sparkfun/SparkFun_Thing_Plus_NORA-W306/docs/more_examples.md

Of course, this only skims the surface of what the SparkFun Thing Plus - NORA-W306 can do. There are a handful of examples from the board support package that were not highlighted in this tutorial and are being ported by our friends at Realtek with the NORA-W306 module. From the menu, try opening the other examples listed for hte board: **File** > **Examples** > <font style="color:gray">Examples for AW_CU488 Thing Plus (RTL8721DM)</font>

<div style="text-align: center;">
  <table>
    <tr style="vertical-align:middle;">
     <td style="text-align: center; vertical-align: middle; border: solid 1px #cccccc;"><a href="../assets/img/AmebaD_RealTek_Additional_Arduino_Examples.JPG">More Arduino Examples!</a></td>
    </tr>
    <tr style="vertical-align:middle;">
     <td style="text-align: center; vertical-align: middle; border: solid 1px #cccccc;"><i>More Arduino Examples!</i></td>
   </tr>
  </table>
</div>

!!! note
    Some of the examples listed in the menu may still be under development. Make sure to be patient as they include more support for the NORA-W306 module.

Or try adding another [Qwiic-enabled device](https://www.sparkfun.com/qwiic) or a breakout board to your next project!

<div style="text-align: center"><a href="https://www.sparkfun.com/qwiic" class="md-button md-button--primary">Qwiic Connect System</a></div>
