sparkfun/SparkFun_Thing_Plus_NORA-W306/docs/github/contribute.md

# Contribute: Help Fix our Mistake!
Spot something wrong? Feel free to contribute our open-source design and documentation. 

## Improve our Documentation
All of this documentation can be modified by you! Please help us make it better.

* These pages are contained in the [`docs` folder of the SparkFun Thing Plus NORA-W306 repository](https://github.com/sparkfun/SparkFun_Thing_Plus_NORA-W306/tree/main/docs).

### Submit a Correction
1. Fork this repo
2. Add your corrections or improvements to the markdown file
3. File a pull request with your changes, and enjoy making the ~~words~~ ~~worlds~~ world a better place.
    * Once received, the documentation specialist will automatically be notified.
    * We will review your suggested improvements to make sure they are correct and fit within our documentation standards.

## Improve our Hardware Design
All of our designs are open-source! Please help us make it better.

* Our board design files are contained in the [`Hardware` folder of the SparkFun Thing Plus NORA-W306 repository](https://github.com/sparkfun/SparkFun_Thing_Plus_NORA-W306/tree/main/Hardware).

### Submit a Design Improvement
1. Fork this repo
2. Add your design improvements
3. File a pull request with your changes, and enjoy making the ~~words~~ ~~worlds~~ world a better place.
    * Once received, the engineer in charge of the original design will automatically be notified.
    * We will review your suggested improvements, if they are within our board design standards and meet our product design requirements, we will flag these changes for our next board revision. *(Please note, that even if your suggestion is accepted, these changes may not be immediate. We may have to cycle through our current product inventory first.)*

## Contributors
Let's provided some recognition to the contributors for this project!

GitHub Contributors Image
<br>
