sparkfun/SparkFun_Thing_Plus_NORA-W306/docs/assets/img/LiPo_Fuel_Gauge_MAX1704X_Qwiic_Cable_Micro_OLED_Output_Display.jpg

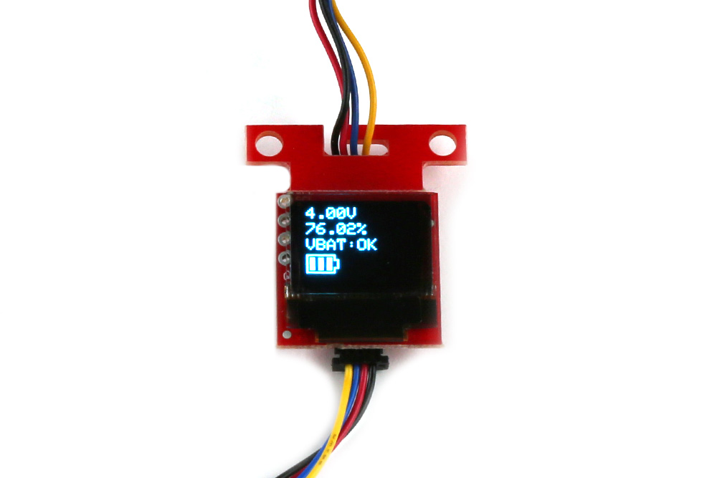
docs/assets/img/LiPo_Fuel_Gauge_MAX1704X_Qwiic_Cable_Micro_OLED_Output_Display.jpg
